daniao2018/sdju_ros_car/开发文档/开发进程/图片/第十周（三）.png

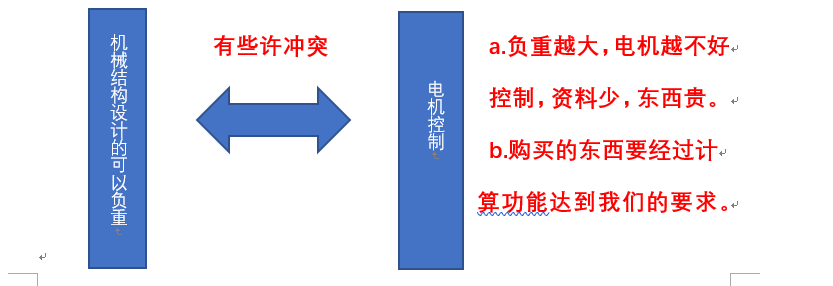
开发文档/开发进程/图片/第十周（三）.png
