daniao2018/sdju_ros_car/开发文档/项目总体/据角钢.jpg

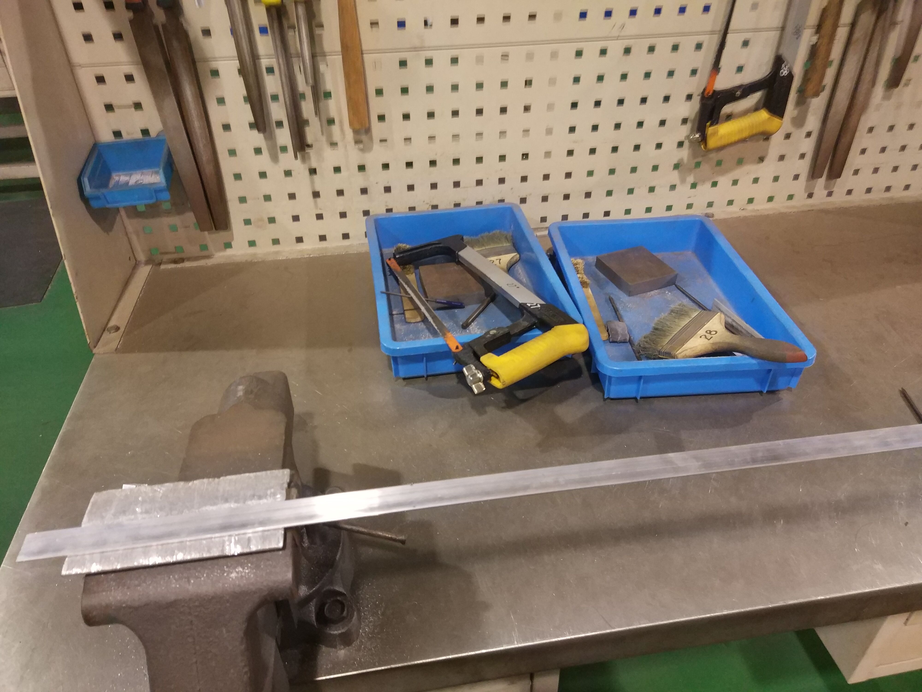
开发文档/项目总体/据角钢.jpg
