daniao2018/sdju_ros_car/开发文档/项目总体/陀螺仪.jpg

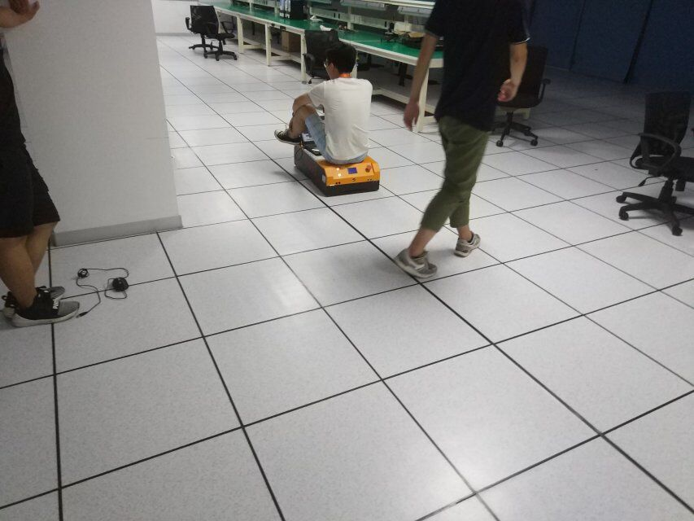
开发文档/项目总体/陀螺仪.jpg
