daniao2018/sdju_ros_car/开发文档/项目申请/ros简介.png

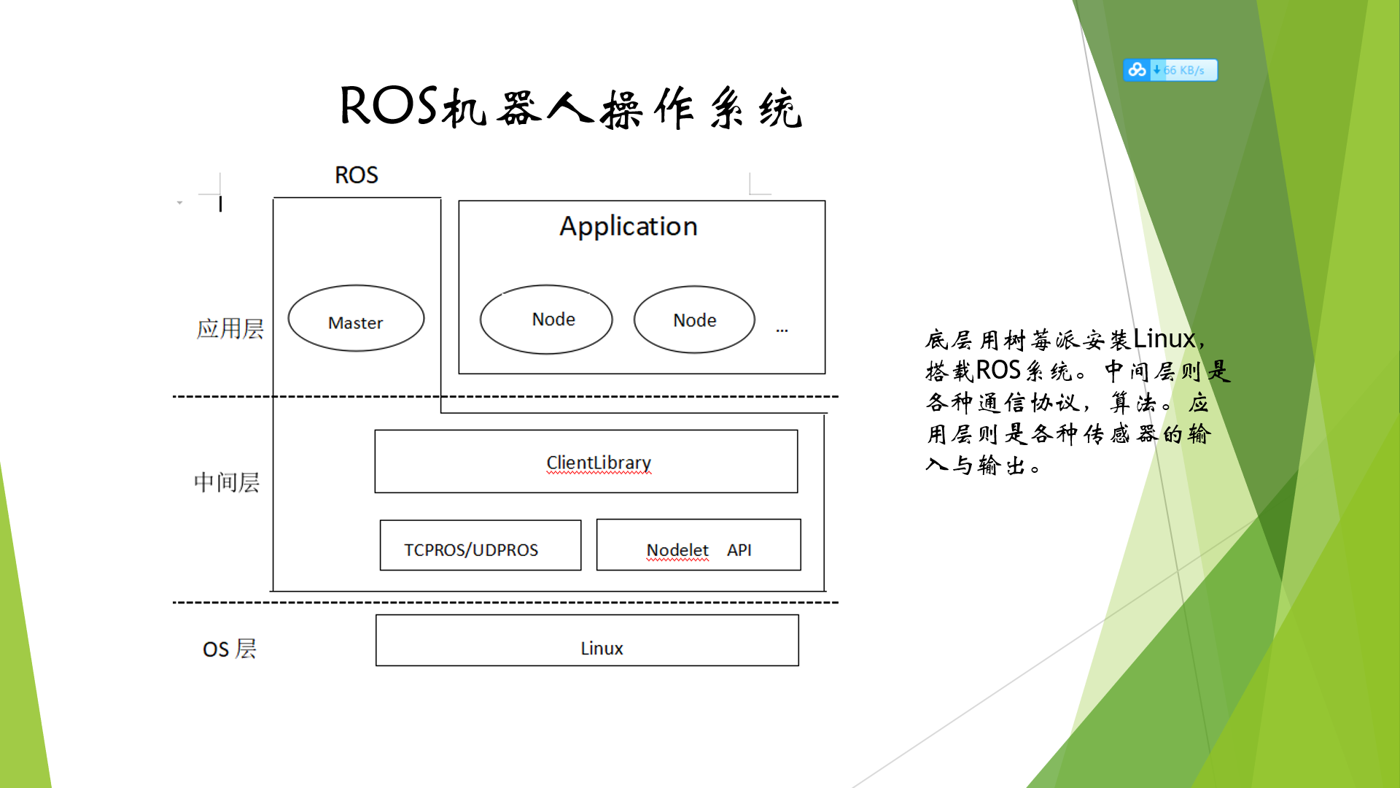
开发文档/项目申请/ros简介.png
