daniao2018/sdju_ros_car/开发文档/项目申请/控制方案.png

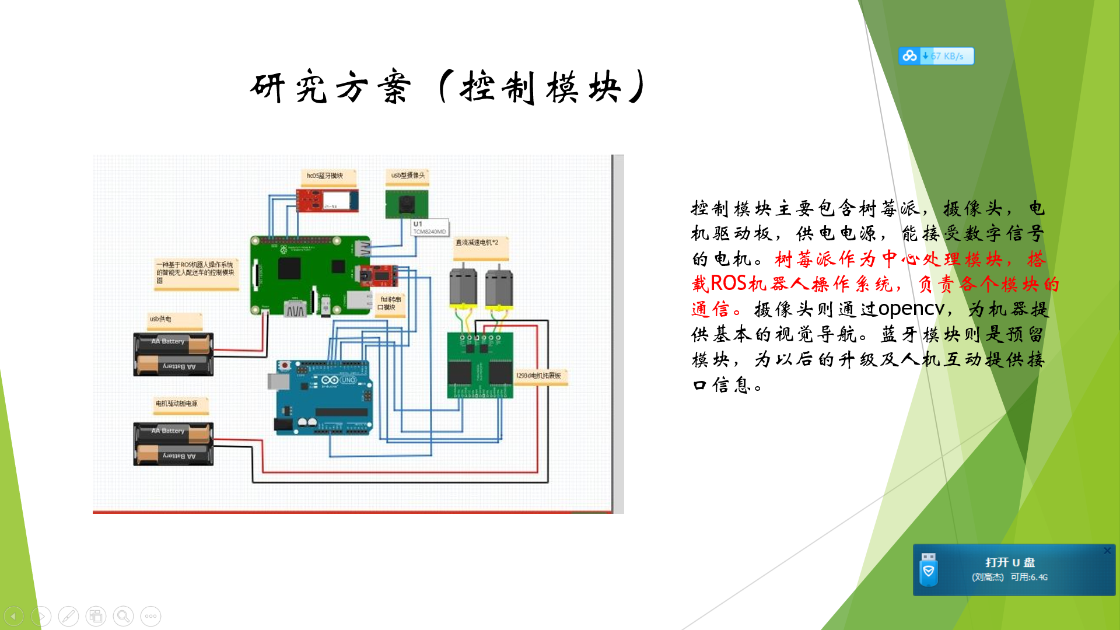
开发文档/项目申请/控制方案.png
