daniao2018/sdju_ros_car/开发文档/项目申请/项目人员.png

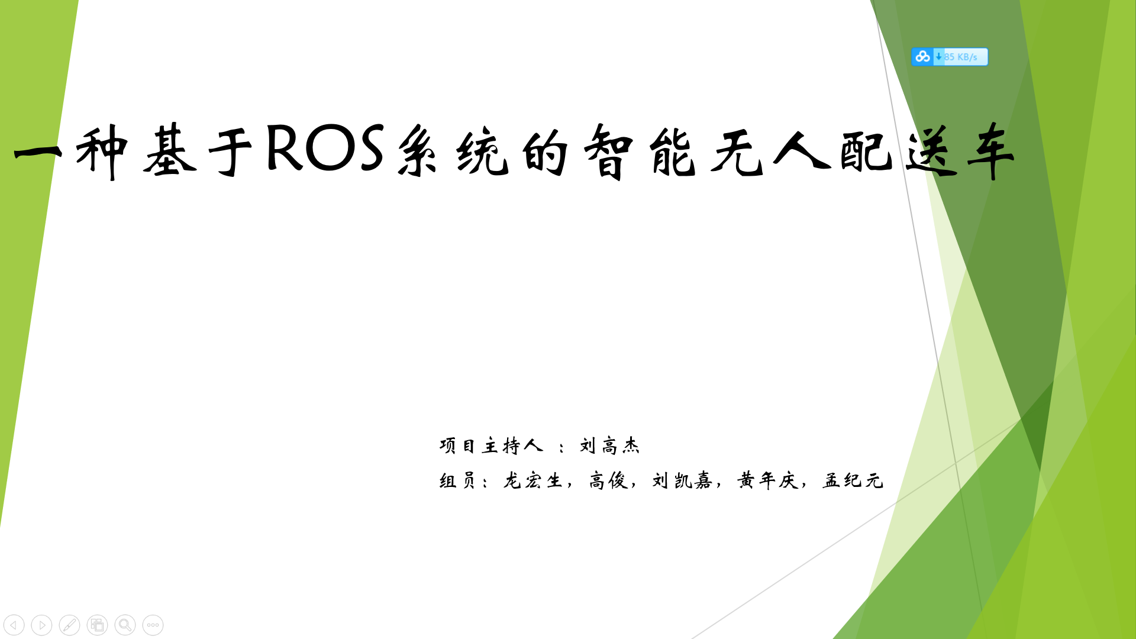
开发文档/项目申请/项目人员.png
