daniao2018/sdju_ros_car/电路部分_F1/电路部分/总体模块图/外置模块电路图_bb.png

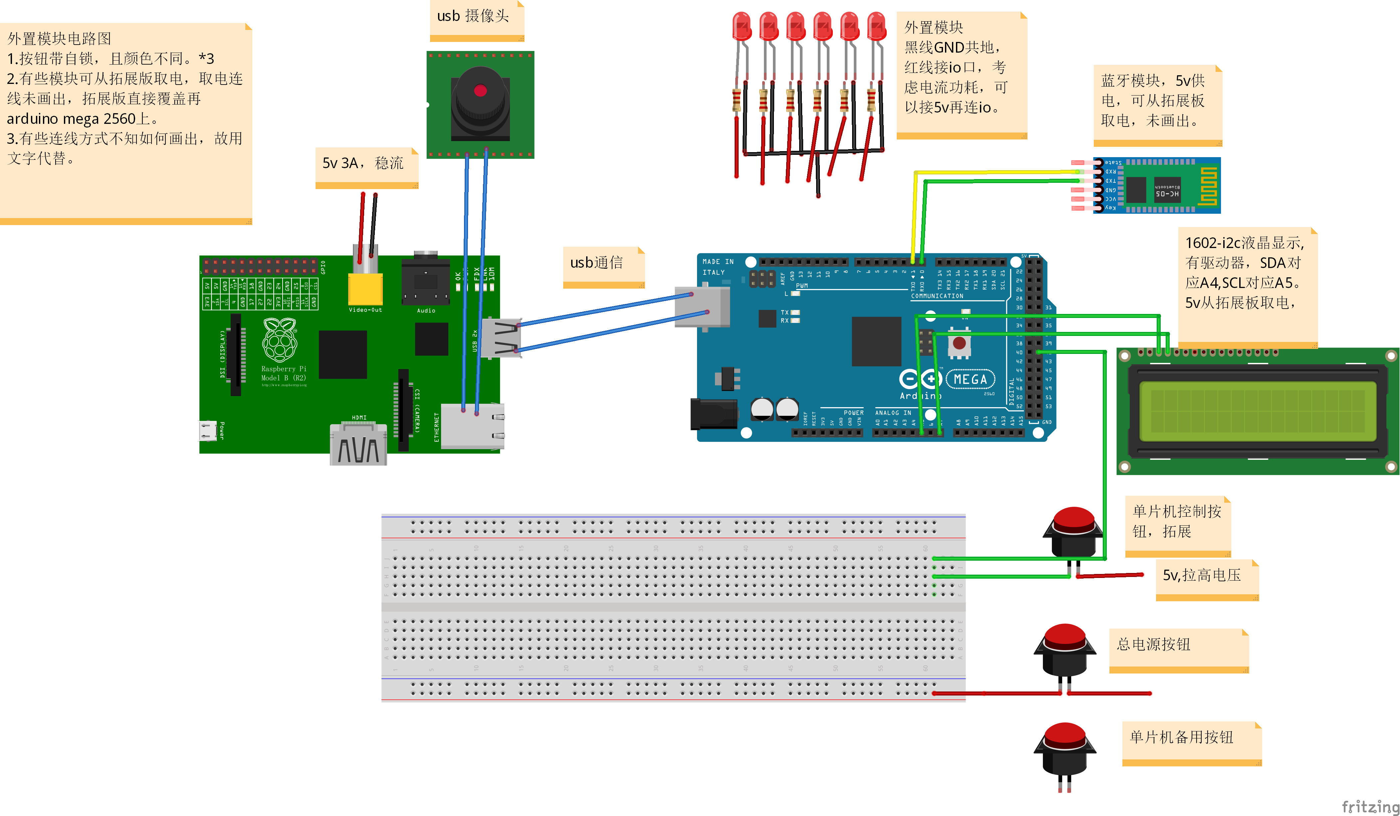
电路部分_F1/电路部分/总体模块图/外置模块电路图_bb.png
