daniao2018/sdju_ros_car/电路部分_F1/电路部分/总体模块图/电源模块_bb.png

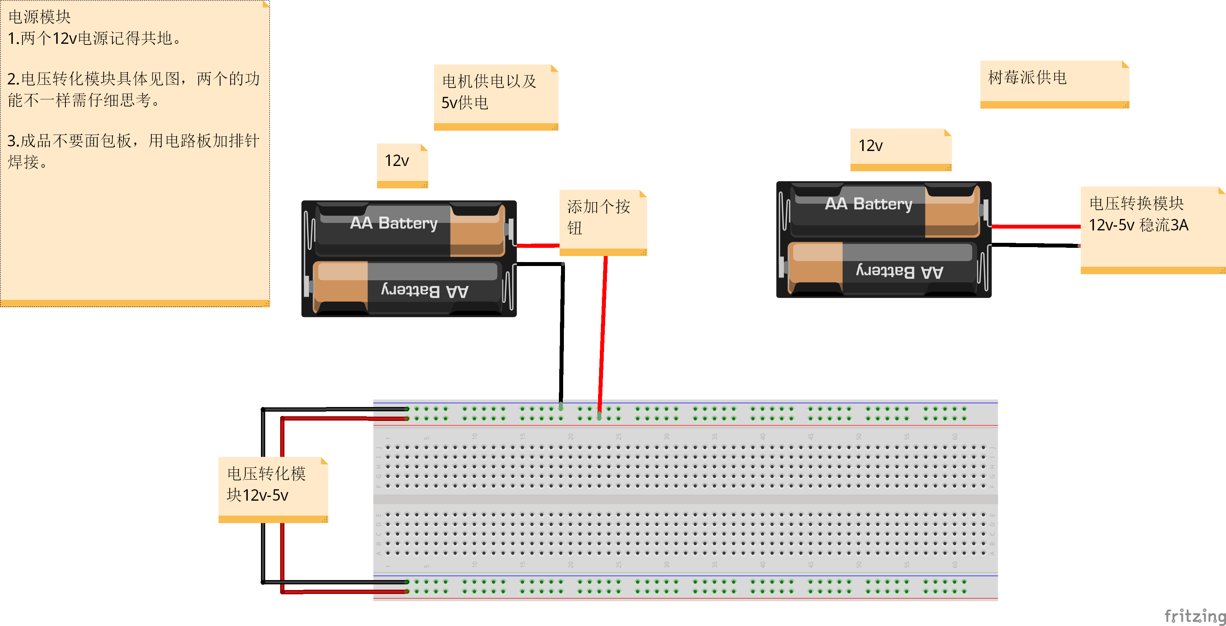
电路部分_F1/电路部分/总体模块图/电源模块_bb.png
