daniao2018/sdju_ros_car/电路部分_F1/电路部分/模块补充图/电机驱动器.png

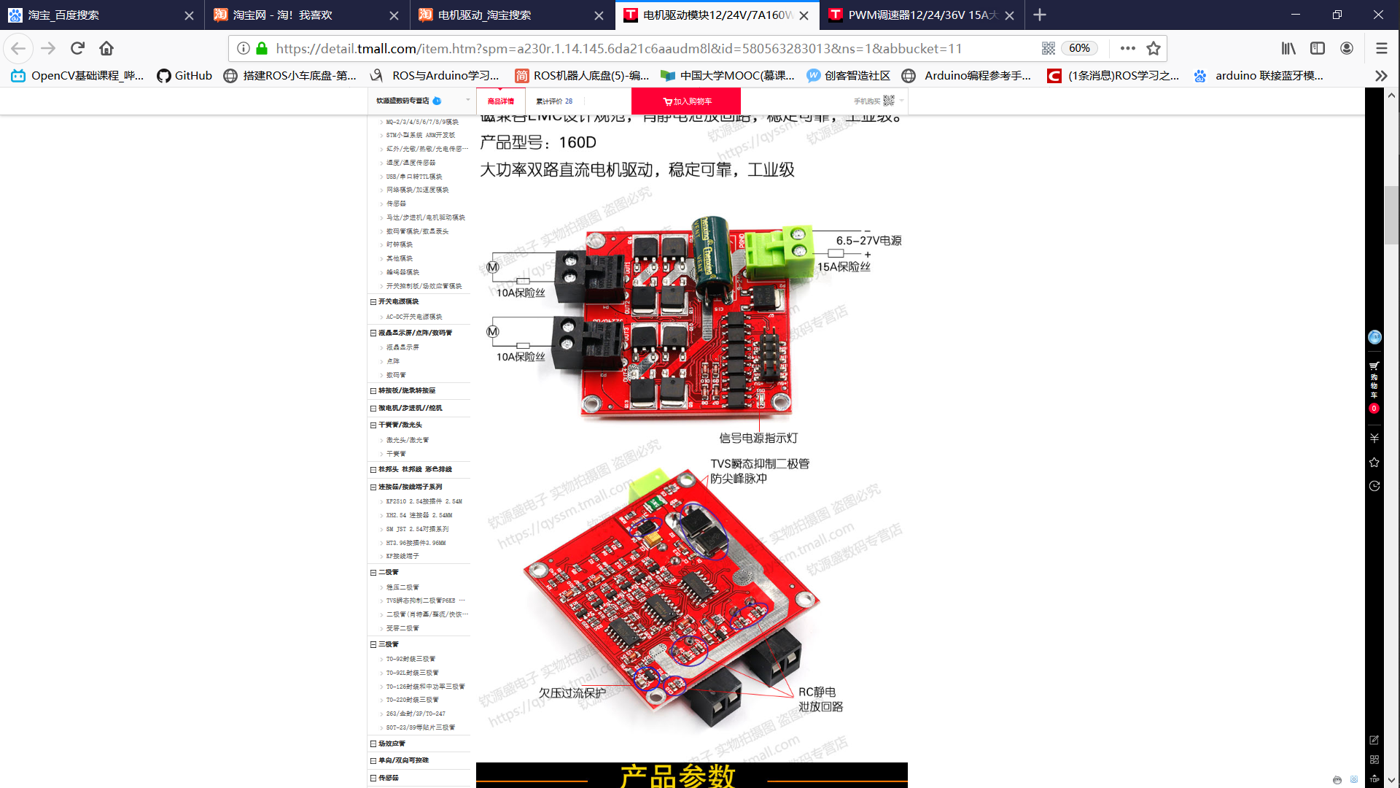
电路部分_F1/电路部分/模块补充图/电机驱动器.png
